Pastitas/Redox-neo-Case/redox_w/step files/Redox_neo_w_adapter-box.step

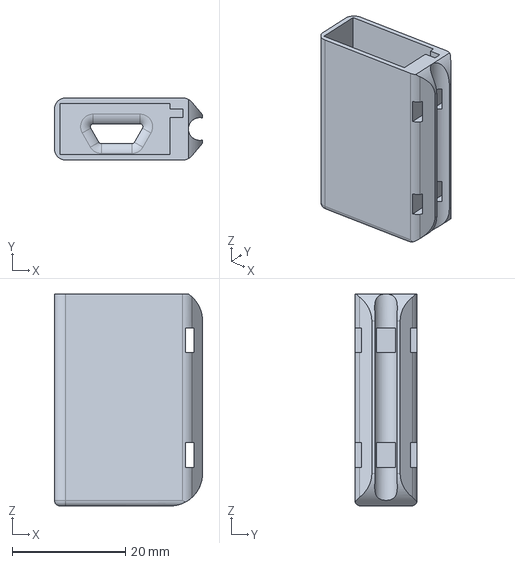
[picture p14: CAD file, 2021-02-16]
redox_w/step files/Redox_neo_w_adapter-box.step
26.2 x 11.0 x 37.5 mm
