Pastitas/Redox-neo-Case/redox_w/step files/Redox_neo_w-Switch-Right.step

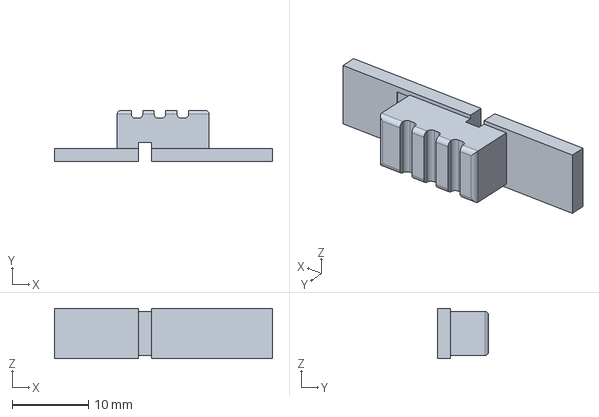
[picture p15: CAD file, 2021-02-16]
redox_w/step files/Redox_neo_w-Switch-Right.step
28.5 x 6.70 x 6.60 mm
