Pastitas/Redox-neo-Case/redox_w/step files/Redox_neo_w_adapter-cover.step

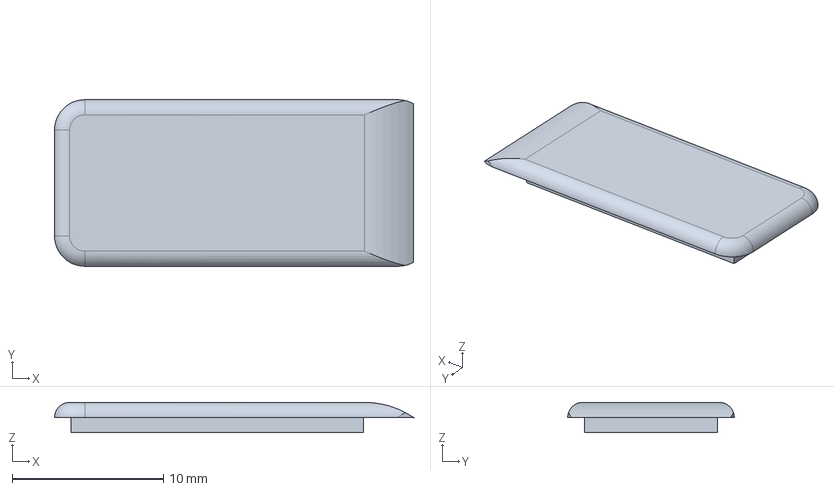
[picture p16: CAD file, 2021-02-16]
redox_w/step files/Redox_neo_w_adapter-cover.step
23.7 x 11.0 x 2.00 mm
